sadekbaroudi/sweep36/cases/swweeep/swweeep-body-covered-widecover-left.step

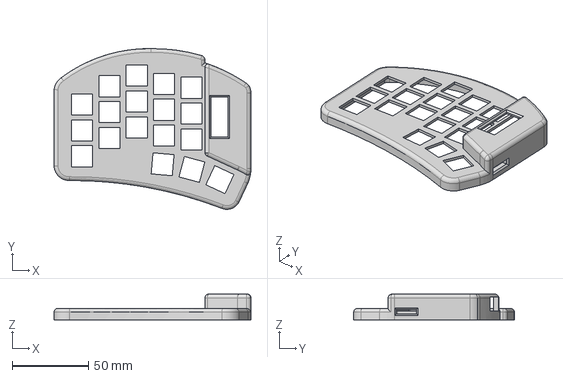
[picture p43: CAD file, 2022-11-05]
cases/swweeep/swweeep-body-covered-widecover-left.step
129.6 x 105.7 x 17.0 mm
