sadekbaroudi/sweep36/cases/swweeep/swweeep-bot-left.step

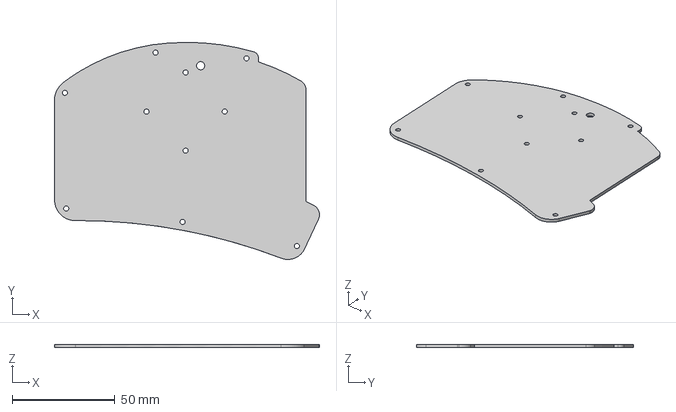
[picture p44: CAD file, 2022-10-27]
cases/swweeep/swweeep-bot-left.step
129.1 x 105.7 x 1.60 mm
