sadekbaroudi/sweep36/cases/swweeep/swweeep-bot-widecover-left.step

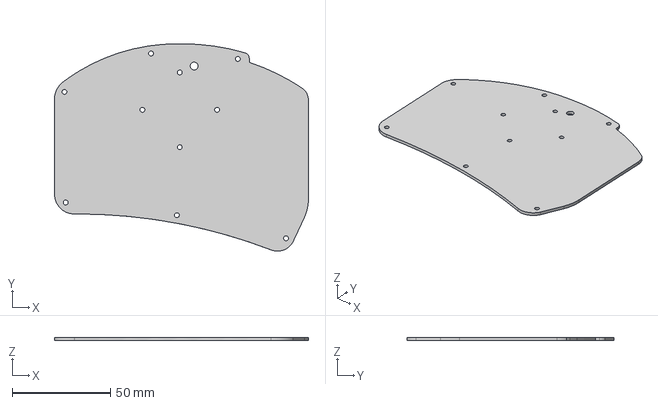
[picture p45: CAD file, 2022-10-27]
cases/swweeep/swweeep-bot-widecover-left.step
129.6 x 105.7 x 1.60 mm
